mrudelle/word-clock/hardware/pcb_jumper/wordclock_pcb_jumber.kicad_sch

## KiCad design hardware/pcb_jumper/wordclock_pcb_jumber.kicad_sch (2023-12-31)

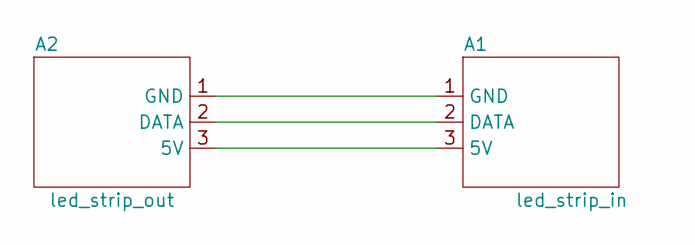
[picture p19: schematic wordclock_pcb_jumber.kicad_sch]

Parts:
A1: led_strip_in; BTFLED-STRIP
A2: led_strip_out; BTFLED-STRIP

Connections:
unnamed: A1.1 (GND), A2.1 (GND)
unnamed: A1.2 (DATA), A2.2 (DATA)
unnamed: A1.3 (5V), A2.3 (5V)
